hexeguitar/PowerMonitor/Pics/pmon1.jpg

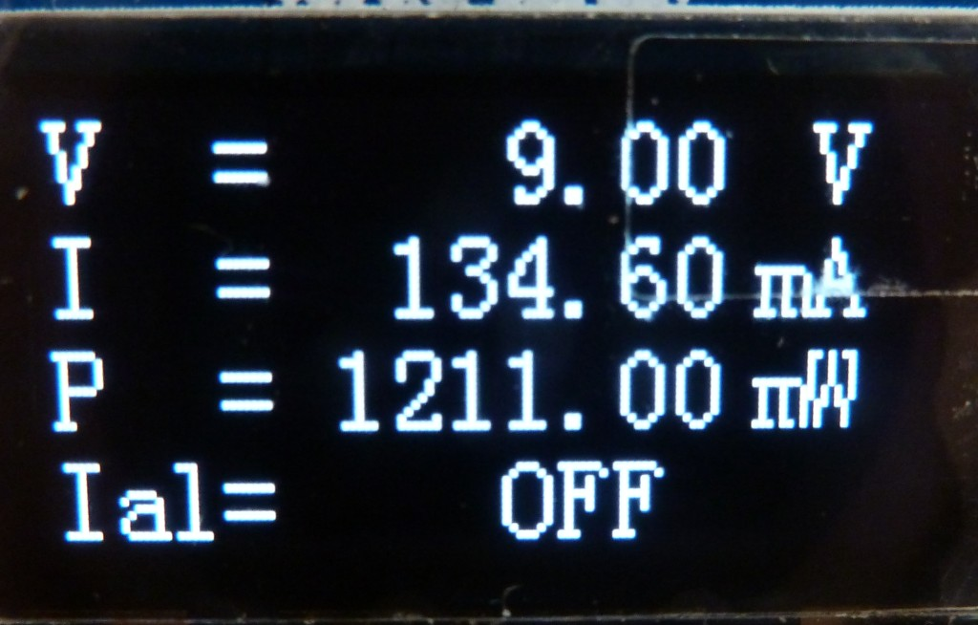
Pics/pmon1.jpg
