hexeguitar/PowerMonitor/Pics/pmon2.jpg

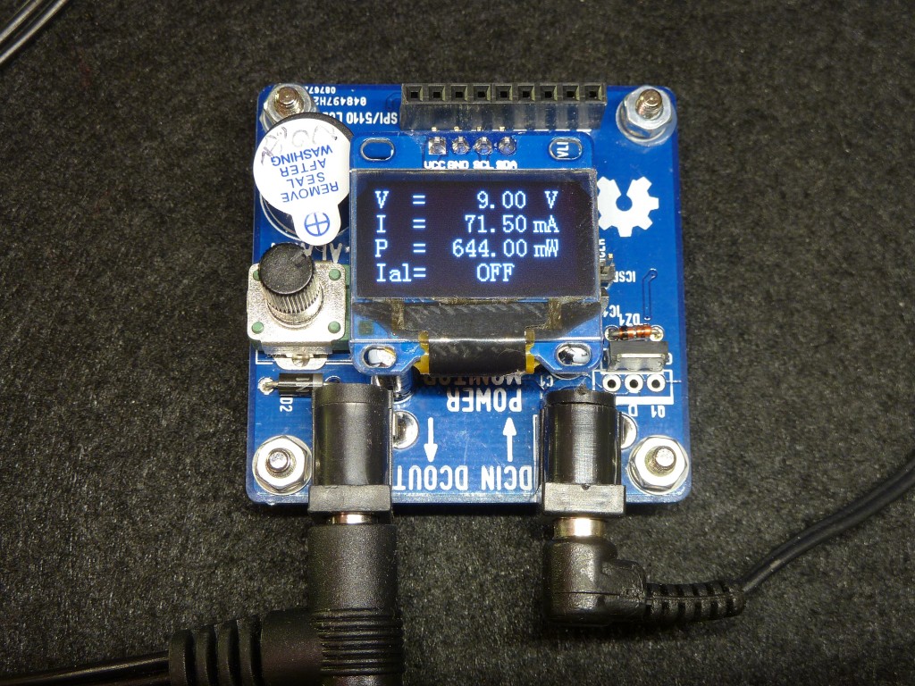
Pics/pmon2.jpg
