hexeguitar/PowerMonitor/Pics/pmon4.jpg

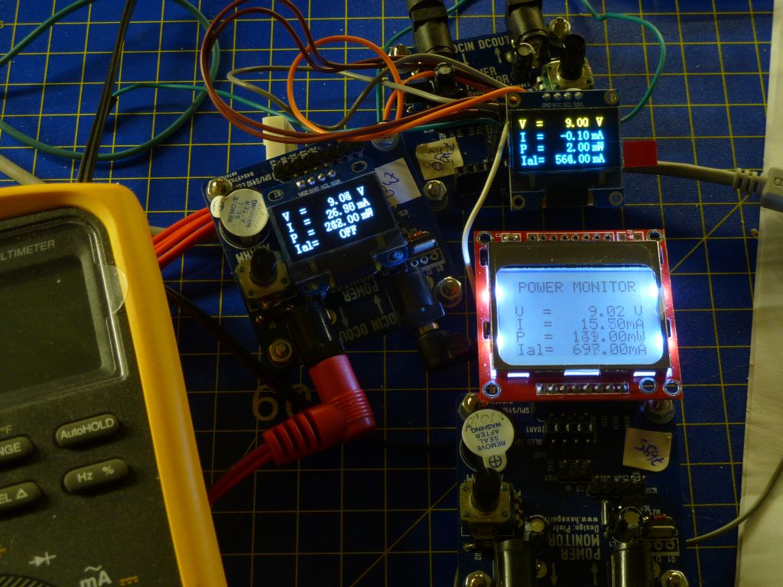
Pics/pmon4.jpg
