hexeguitar/PowerMonitor/Pics/pmon6.jpg

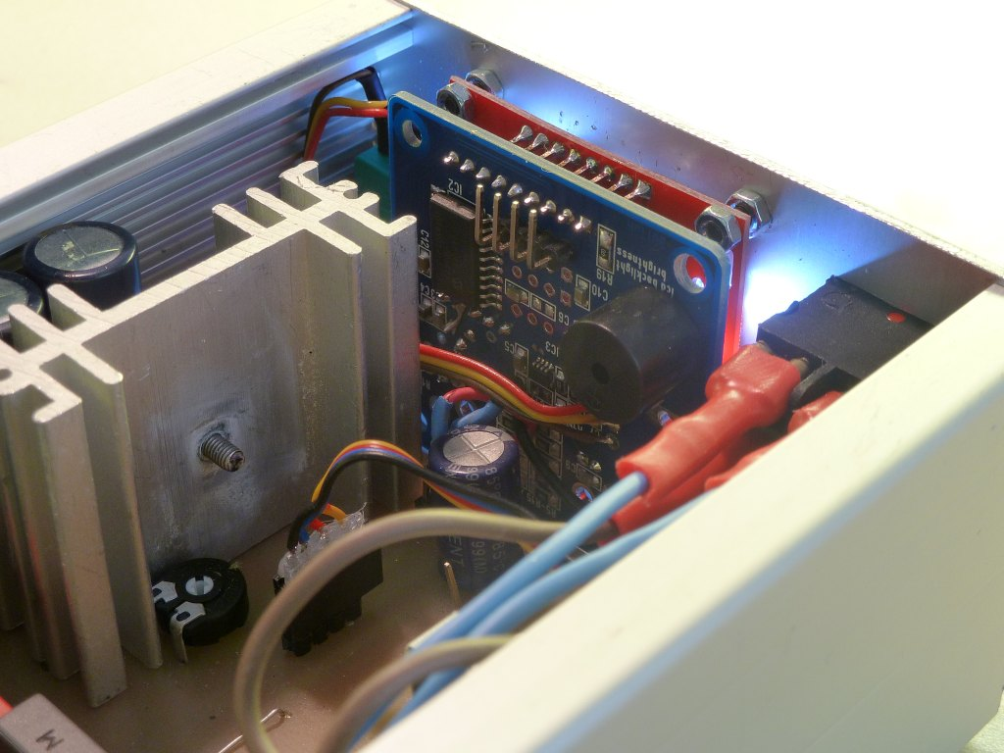
Pics/pmon6.jpg
