hexeguitar/PowerMonitor/Pics/pmon8.jpg

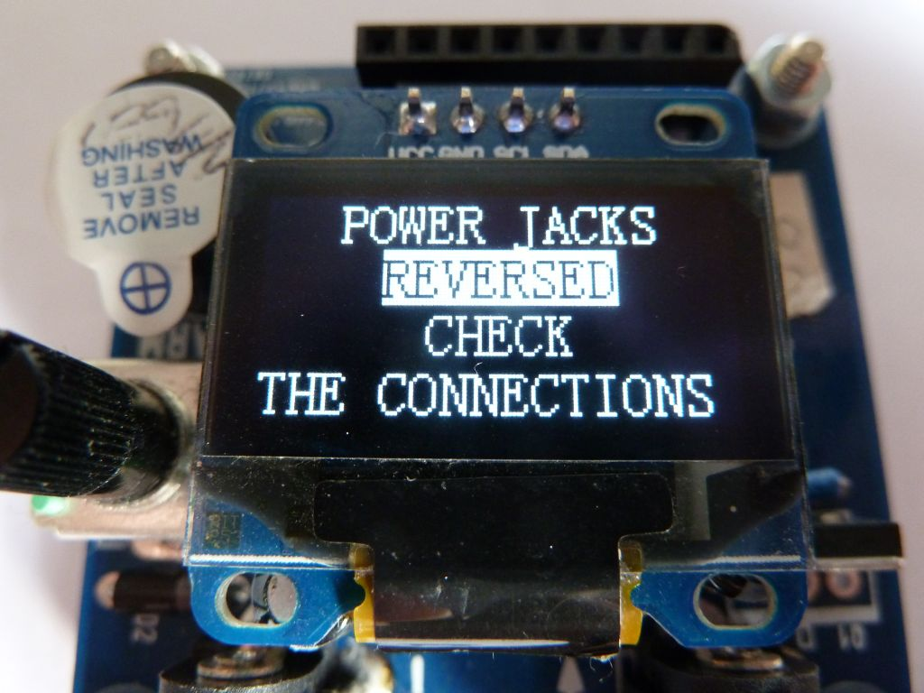
Pics/pmon8.jpg
