hexeguitar/PowerMonitor/Firmware/Sources/Inc/bmp.h

/*
 * bmp.h
 *
 *  Created on: 30.03.2014
 *      Author: Piotr Zapart
 *              www.hexeguitar.com
 */

#ifndef BMP_H_
#define BMP_H_

const unsigned char start_screen[] = { 

 0x00,0x00,0x80,0xE0,0x70,0x38,0x18,0x8C,0xCC,0x46,0x26,0x26,0x26,0x06,0x06,0x06 ,
 0x06,0x06,0x06,0x06,0x06,0x06,0x06,0x06,0x06,0x06,0x06,0x06,0x06,0x06,0x06,0x06 ,
 0x06,0x06,0x06,0x06,0x06,0x06,0x06,0x06,0x06,0x06,0x06,0x06,0x06,0x06,0x06,0x06 ,
 0x06,0x06,0x06,0x06,0x06,0x06,0x06,0x06,0x06,0x06,0x06,0x06,0x06,0x06,0x06,0x06 ,
 0x06,0x06,0x06,0x06,0x06,0x06,0x06,0x06,0x06,0x06,0x06,0x06,0x06,0x06,0x06,0x06 ,
 0x06,0x06,0x06,0x06,0x06,0x06,0x06,0x06,0x06,0x06,0x06,0x06,0x06,0x06,0x06,0x06 ,
 0x06,0x06,0x06,0x06,0x06,0x06,0x06,0x06,0x06,0x06,0x06,0x06,0x06,0x06,0x06,0x06 ,
 0x06,0x06,0x06,0x06,0x06,0x06,0x06,0x0C,0x0C,0x18,0x38,0x70,0xE0,0x80,0x00,0x00 ,
 0x00,0xFE,0xFF,0x01,0x00,0x00,0x0E,0x01,0x00,0x00,0x00,0x00,0xFE,0xFE,0x42,0x42 ,
 0x42,0x7E,0x3C,0x00,0xF8,0xFC,0x06,0x02,0x06,0xFC,0xF8,0x1E,0xFE,0x80,0x78,0x78 ,
 0xC0,0xFE,0x1E,0x00,0xFE,0xFE,0x22,0x22,0x22,0x22,0x02,0x00,0xFE,0xFE,0x42,0x42 ,
 0xC2,0xBE,0x3C,0x00,0x00,0x00,0x00,0x00,0x00,0x00,0x00,0x00,0xFE,0xFE,0x3E,0x60 ,
 0x3E,0xFE,0xFE,0x00,0xF8,0xFC,0x06,0x02,0x06,0xFC,0xF8,0x00,0xFE,0xFE,0x1E,0x70 ,
 0xC0,0xFE,0xFE,0x00,0x02,0x02,0xFE,0xFE,0x02,0x02,0x00,0x00,0x02,0x02,0xFE,0xFE ,
 0x02,0x02,0x00,0x00,0xF8,0xFC,0x06,0x02,0x06,0xFC,0xF8,0x00,0xFE,0xFE,0x42,0x42 ,
 0xC2,0xBE,0x3C,0x00,0x00,0x00,0x00,0x00,0x00,0x00,0x00,0x00,0x01,0xFF,0xFE,0x00 ,
 0x00,0xFF,0xFF,0x00,0x00,0x00,0x00,0x00,0x00,0x00,0x00,0x00,0x03,0x03,0x00,0x00 ,
 0x00,0x00,0x00,0x00,0x00,0x01,0x03,0x02,0x03,0x01,0x00,0x00,0x03,0x03,0x00,0x00 ,
 0x03,0x03,0x00,0x00,0x03,0x03,0x02,0x02,0x02,0x02,0x02,0x00,0x03,0x03,0x00,0x00 ,
 0x00,0x01,0x03,0x02,0x00,0x00,0x00,0x00,0x00,0x00,0x00,0xC0,0xC3,0xC3,0xC0,0x00 ,
 0x00,0x03,0x03,0x00,0x00,0x01,0x03,0x02,0x03,0x01,0x00,0x00,0x03,0x03,0x00,0x00 ,
 0x03,0x03,0x03,0x00,0x02,0x02,0x03,0x03,0x02,0x02,0x00,0x00,0x00,0x00,0x03,0x03 ,
 0x00,0x00,0x00,0x00,0x00,0x01,0x03,0x02,0x03,0x01,0x00,0x00,0x03,0x03,0x00,0x00 ,
 0x00,0x01,0x03,0x02,0x00,0x00,0x00,0x00,0x00,0x00,0x00,0x00,0x00,0xFF,0xFF,0x00 ,
 0x00,0xFF,0xFF,0x00,0x00,0x00,0x00,0x00,0x00,0x00,0x00,0x00,0x00,0x00,0x00,0x00 ,
 0x00,0x00,0x00,0x00,0x00,0x00,0x00,0x00,0x00,0x00,0x00,0x00,0x00,0x00,0x00,0x00 ,
 0x00,0x00,0x00,0x00,0x00,0x00,0x00,0x00,0x00,0x00,0x00,0x00,0x00,0x00,0x00,0x00 ,
 0x80,0xC0,0xF0,0xF8,0xFC,0x7C,0x3E,0x1E,0x1E,0x00,0x00,0xFF,0xFF,0xFF,0xFF,0x00 ,
 0x00,0x1E,0x1E,0x3E,0x7C,0xFC,0xF8,0xF0,0xC0,0x80,0x00,0x00,0x00,0x00,0x00,0x00 ,
 0x00,0x00,0x00,0x00,0x00,0x00,0x00,0x00,0x00,0x00,0x00,0x00,0x00,0x00,0x00,0x00 ,
 0x00,0x00,0x00,0x00,0x00,0x00,0x00,0x00,0x00,0x00,0x00,0x00,0x00,0x00,0x00,0x00 ,
 0x00,0x00,0x00,0x00,0x00,0x00,0x00,0x00,0x00,0x00,0x00,0x00,0x00,0xFF,0xFF,0x00 ,
 0x00,0xFF,0xFF,0x00,0x00,0x00,0x00,0x00,0x00,0x00,0x00,0x00,0x00,0x00,0x00,0x00 ,
 0x00,0x00,0x00,0x00,0x00,0x00,0x00,0x00,0x00,0x00,0x00,0x00,0x00,0x00,0x00,0x00 ,
 0x00,0x00,0x00,0x00,0x00,0x00,0x00,0x00,0x00,0x00,0x00,0x00,0x00,0x00,0x00,0x00 ,
 0xFF,0xFF,0xFF,0xFF,0x00,0x00,0x00,0x00,0x00,0x00,0x00,0x1F,0x1F,0x1F,0x1F,0x00 ,
 0x00,0x00,0x00,0x00,0x00,0x00,0xFF,0xFF,0xFF,0xFF,0x00,0x00,0x00,0x00,0x00,0x00 ,
 0x00,0x00,0x00,0x00,0x00,0x00,0x00,0x00,0x00,0x00,0x00,0x00,0x00,0x00,0x00,0x00 ,
 0x00,0x00,0x00,0x00,0x00,0x00,0x00,0x00,0x00,0x00,0x00,0x00,0x00,0x00,0x00,0x00 ,
 0x00,0x00,0x00,0x00,0x00,0x00,0x00,0x00,0x00,0x00,0x00,0x00,0x00,0xFF,0xFF,0x00 ,
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

};


#endif /* BMP_H_ */
