hexeguitar/PowerMonitor/Firmware/Sources/Inc/converter.h

/* 
 * File:   converter.h
 * Author: Pio
 *
 * Created on 8. Juli 2014, 12:46
 */

#ifndef CONVERTER_H
#define	CONVERTER_H

void f_to_txt(float f_num, char *buf_ptr);
void int_to_txt(int i_num,uint8_t len, char *buf_ptr);
void reverse(char *s);

#endif	/* CONVERTER_H */
