hexeguitar/PowerMonitor/Firmware/Sources/Inc/stdint.h

#ifndef __STDINT_H_
#define __STDINT_H_

typedef signed char int8_t;
typedef unsigned char uint8_t;
typedef signed int int16_t;
typedef unsigned int uint16_t;
typedef signed long  int32_t;
typedef unsigned long uint32_t;
typedef signed long long int int64_t;
typedef unsigned long long int uint64_t;

#define _BV(x)   (1 << x) 

#endif
