hexeguitar/PowerMonitor/Firmware/Sources/Inc/txt.h

/* 
 * File:   txt.h
 * Author:  Piotr Zapart
 *          www.hexeguitar.com
 * Created on 8. Juli 2014, 11:11
 */

#ifndef TXT_H
#define	TXT_H
const char pwmon_txt[]= "POWER MONITOR";
const char link_txt[] = "hexeguitar.com";
const char version[] = "v. 1.0";
const char vbus_txt[] = "V  =";
const char volts_txt[] = " V";
const char current_txt[] = "I  =";
const char mA_txt[] = "mA";
const char power_txt [] = "P  =";
const char mW_txt[] = "mW";
const char curr_al_txt[] = "Ial=";
const char off_txt[] = "    OFF   ";

const char sep_char[] = ";";

const char format_raw_txt[] = "DATA FORMAT = RAW";
const char format_lcd_txt[] = "DATA FORMAT = LCD";


const char warning1_txt[] = "POWER JACKS";
const char warning2_txt[] = "REVERSED";
const char warning3_txt[] = "CHECK";
const char warning4_txt[] = "THE";
const char warning5_txt[] = "CONNECTIONS";

const char rst_txt[] = "RESTORE";
const char cal_txt[] = "CALIBRATION";
const char save_txt[] = "Save? ";
const char yn_txt[] = "y/n";
const char inacal_txt[] = "INA219 CAL=";
const char new_txt[] = "NEW ";
const char old_txt[] = "OLD ";
const char enter_I_txt[] = "Enter the measured value [xxxx.xx]mA:";
const char error_txt [] = "Error: ";
const char err_oor_txt[] = "out of range";
const char iref_txt[] = "Iref";
const char he_txt[] = "????.??";



#endif	/* TXT_H */
